ToniBiro/WALL-E/3D Parts/Other/crateCornerSmall v2.stl

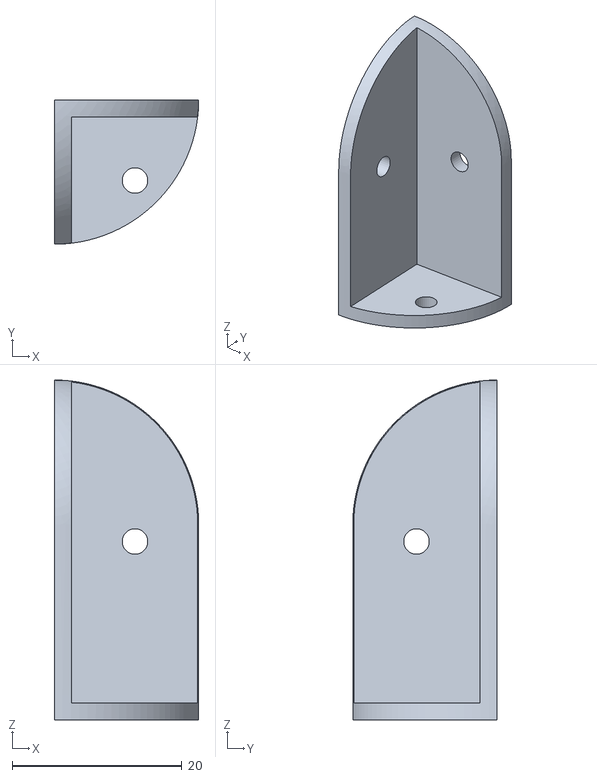
[picture p29: CAD file, 2020-02-20]
3D Parts/Other/crateCornerSmall v2.stl
17.0 x 17.0 x 40.0
