ToniBiro/WALL-E/3D Parts/Other/Text/dot.stl

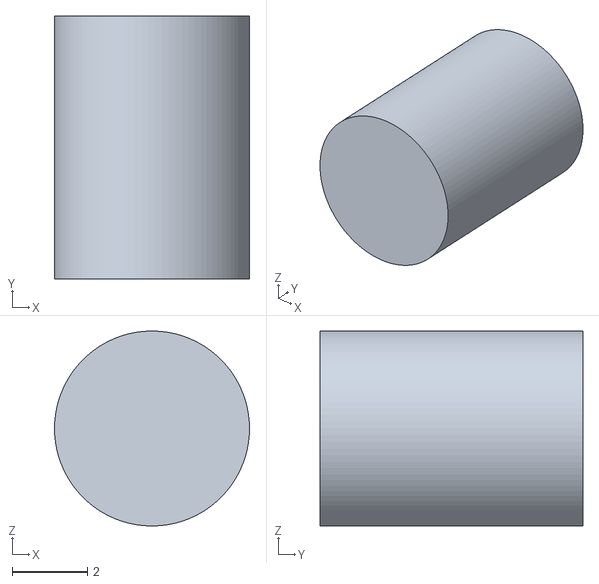
[picture p30: CAD file, 2020-02-20]
3D Parts/Other/Text/dot.stl
5.19 x 7.00 x 5.19
