ToniBiro/WALL-E/3D Parts/Tracks/TractionGear.stl

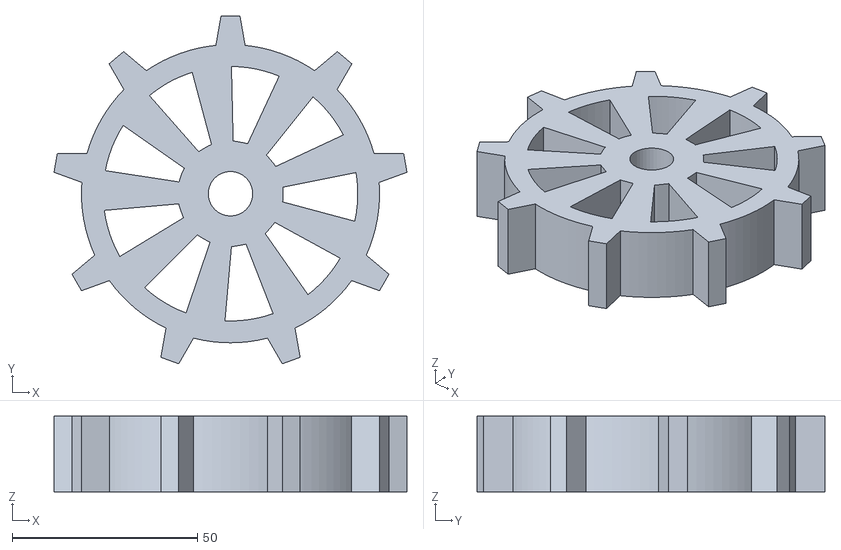
[picture p31: CAD file, 2020-02-19]
3D Parts/Tracks/TractionGear.stl
95.3 x 93.8 x 20.5
