ToniBiro/WALL-E/3D Parts/Arm/ArmMotorHolder.stl

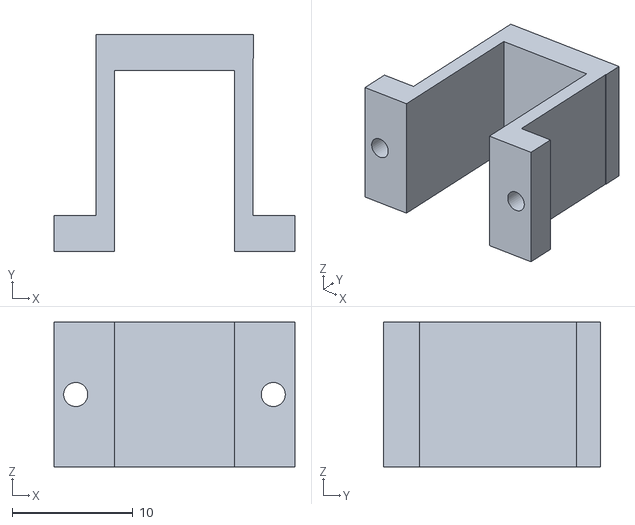
[picture p32: CAD file, 2020-02-19]
3D Parts/Arm/ArmMotorHolder.stl
20.0 x 18.0 x 12.0
