ToniBiro/WALL-E/3D Parts/Compression/FloorWithHinge.stl

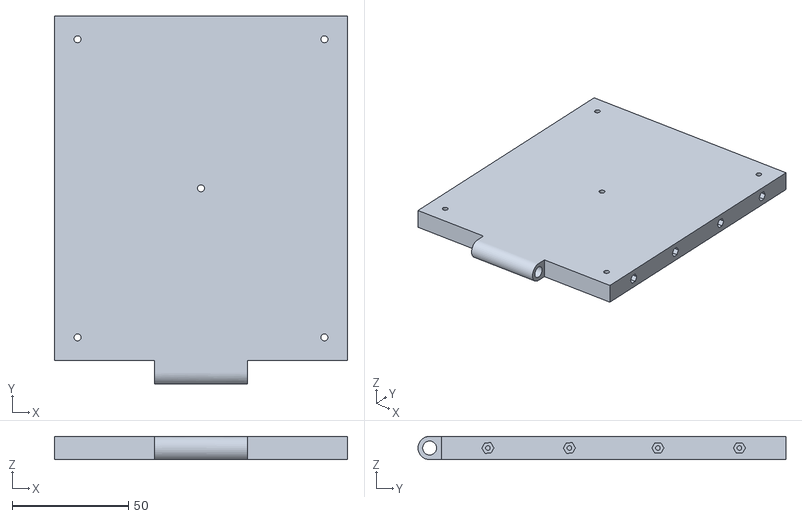
[picture p33: CAD file, 2020-02-19]
3D Parts/Compression/FloorWithHinge.stl
126.0 x 158.0 x 10.0
