ToniBiro/WALL-E/3D Parts/Hand/ConnectionToCilinder.stl

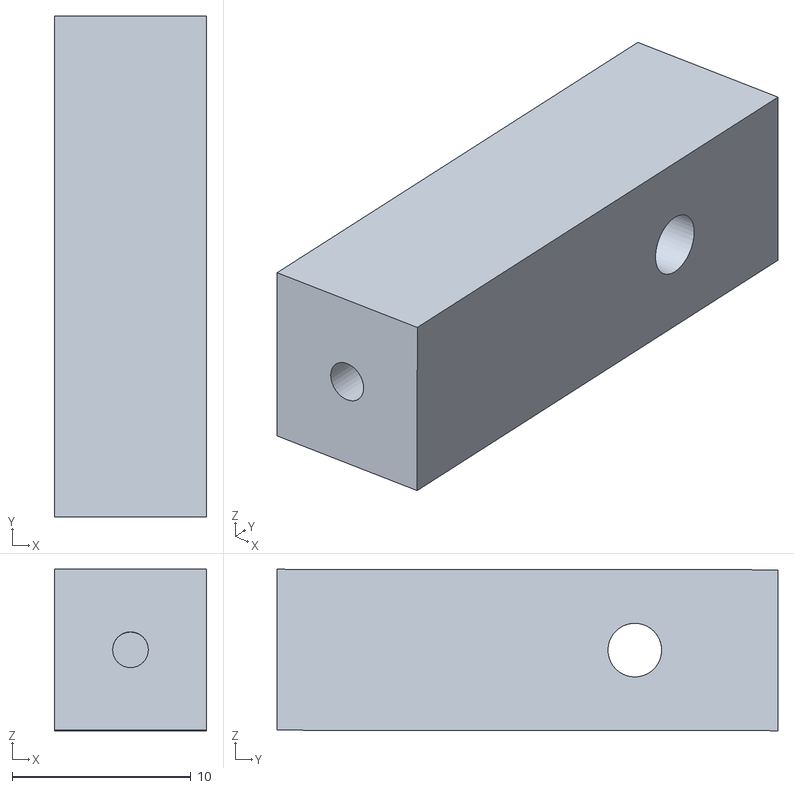
[picture p34: CAD file, 2020-02-19]
3D Parts/Hand/ConnectionToCilinder.stl
8.50 x 28.0 x 9.03
