ToniBiro/WALL-E/3D Parts/Head/connectionCilinderSide.stl

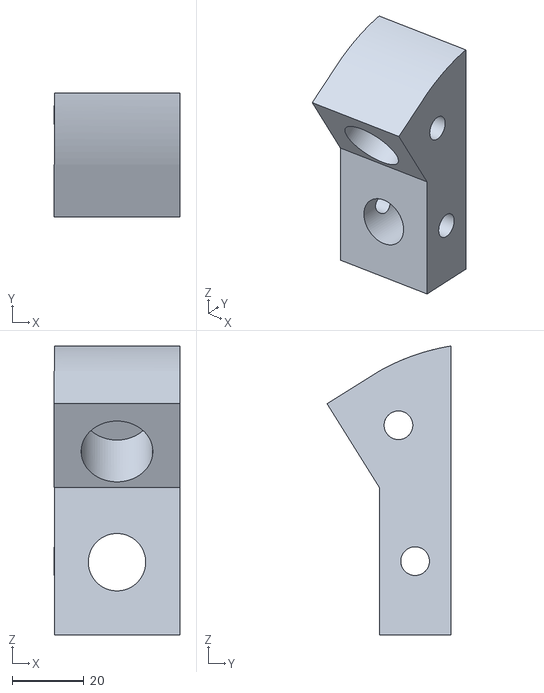
[picture p35: CAD file, 2020-02-19]
3D Parts/Head/connectionCilinderSide.stl
35.0 x 34.6 x 80.6
