ToniBiro/WALL-E/3D Parts/Other/Text/W.stl

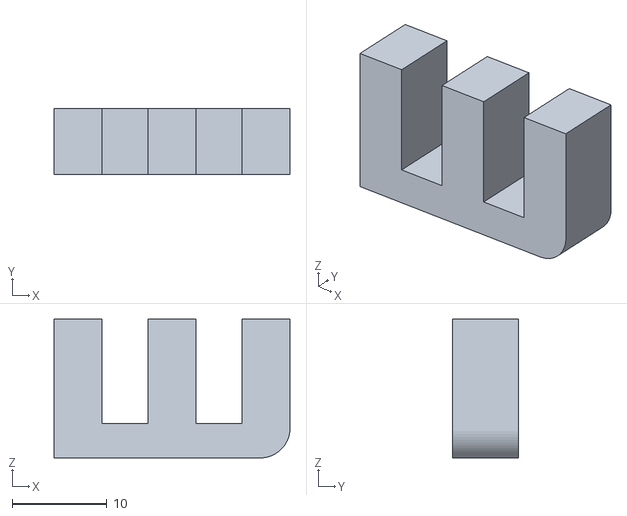
[picture p36: CAD file, 2020-02-20]
3D Parts/Other/Text/W.stl
24.9 x 7.00 x 14.6
