ToniBiro/WALL-E/3D Parts/Tracks/trackPiece.stl

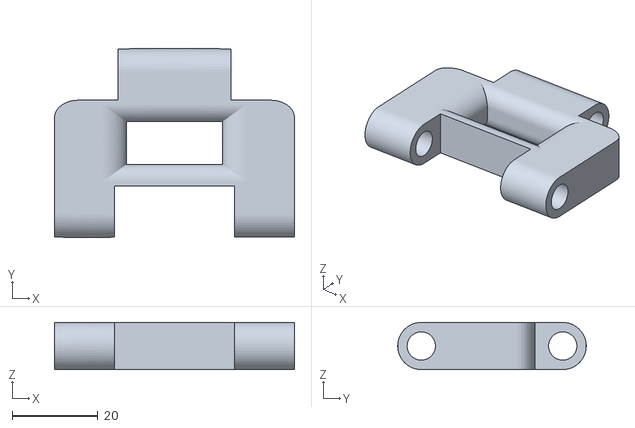
[picture p37: CAD file, 2020-02-19]
3D Parts/Tracks/trackPiece.stl
56.0 x 44.0 x 11.0
