ToniBiro/WALL-E/3D Parts/Arm/MotorCoupling.stl

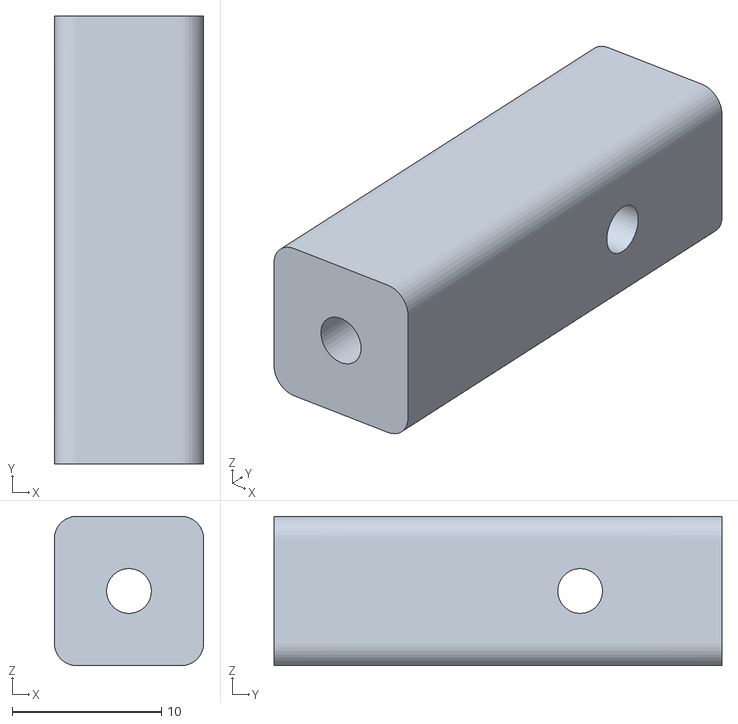
[picture p38: CAD file, 2020-02-19]
3D Parts/Arm/MotorCoupling.stl
10.0 x 30.0 x 10.0
