ToniBiro/WALL-E/3D Parts/Hand/ThirdFinger.stl

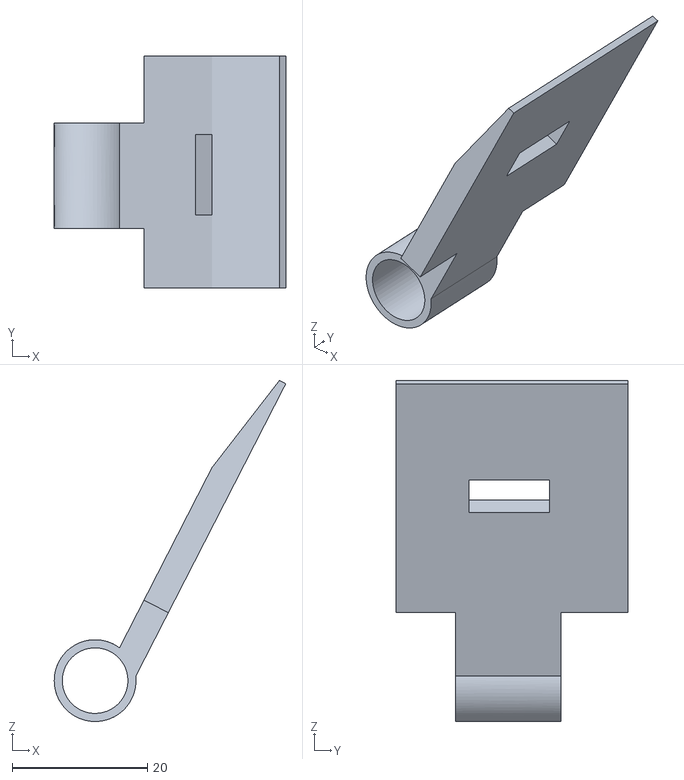
[picture p40: CAD file, 2020-02-19]
3D Parts/Hand/ThirdFinger.stl
34.2 x 34.2 x 50.3
