ToniBiro/WALL-E/3D Parts/Head/connection.stl

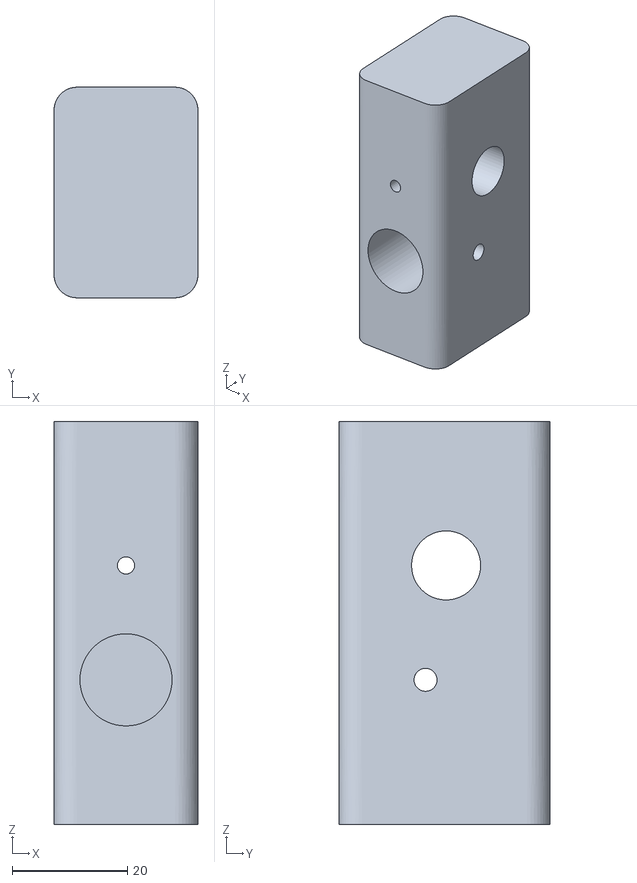
[picture p41: CAD file, 2020-02-19]
3D Parts/Head/connection.stl
25.0 x 36.6 x 70.0
