ToniBiro/WALL-E/3D Parts/Other/Text/L.stl

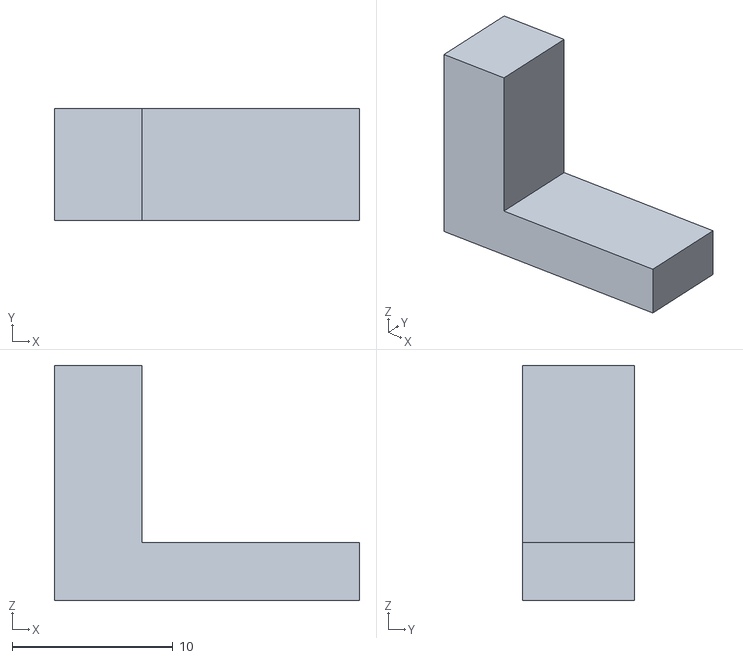
[picture p42: CAD file, 2020-02-20]
3D Parts/Other/Text/L.stl
19.0 x 7.00 x 14.6
