ToniBiro/WALL-E/3D Parts/Tracks/reinforcementTrackGuard.stl

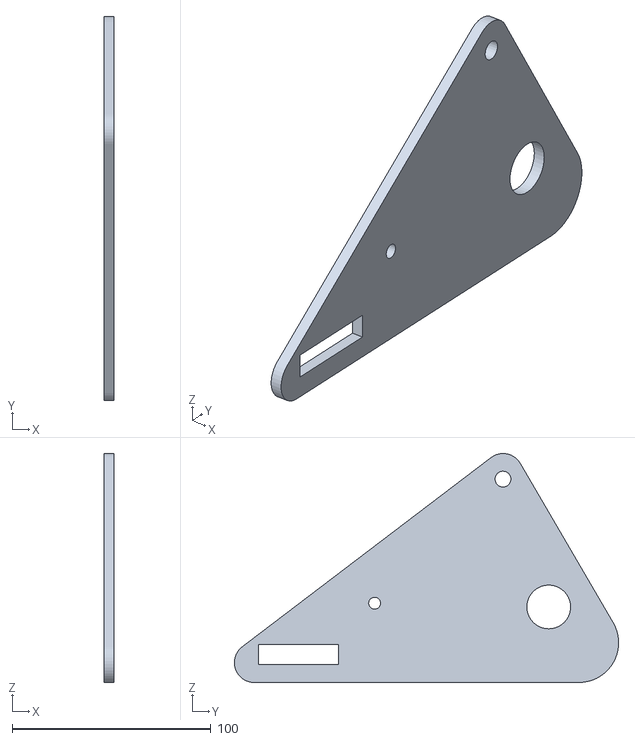
[picture p43: CAD file, 2020-02-19]
3D Parts/Tracks/reinforcementTrackGuard.stl
5.00 x 193.3 x 115.2
