ToniBiro/WALL-E/3D Parts/Arm/LeftArmCoup.stl

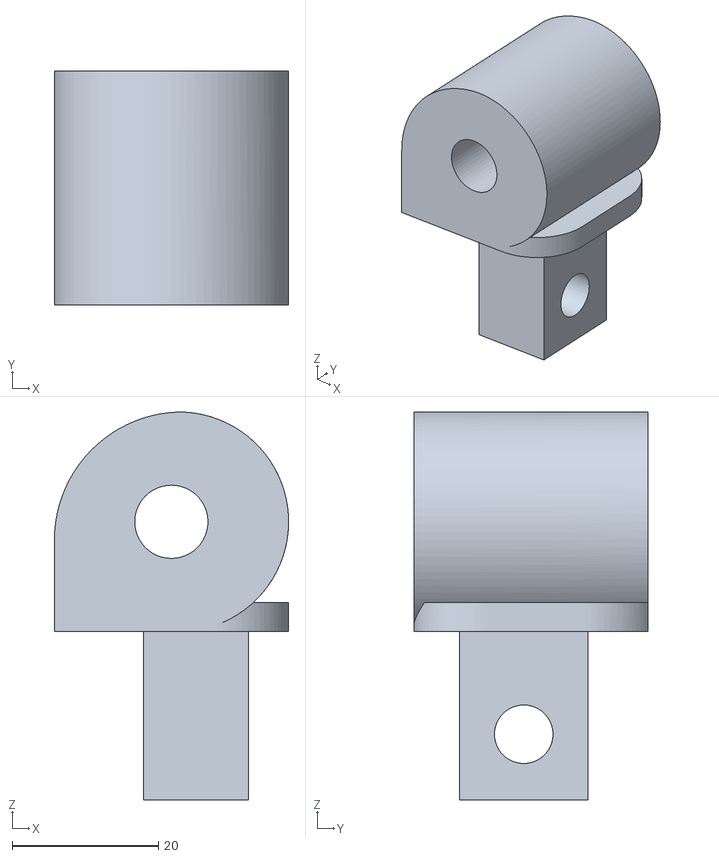
[picture p44: CAD file, 2020-02-19]
3D Parts/Arm/LeftArmCoup.stl
32.0 x 32.0 x 53.0
