ToniBiro/WALL-E/3D Parts/Compression/leftWall.stl

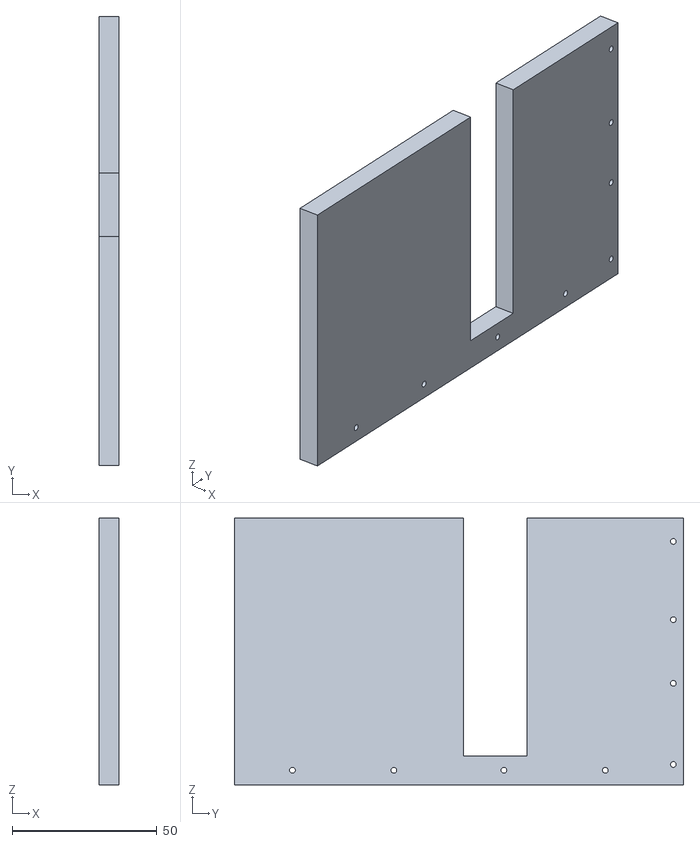
[picture p45: CAD file, 2020-02-19]
3D Parts/Compression/leftWall.stl
7.00 x 155.0 x 92.0
