ToniBiro/WALL-E/3D Parts/Head/bodyConnection.stl

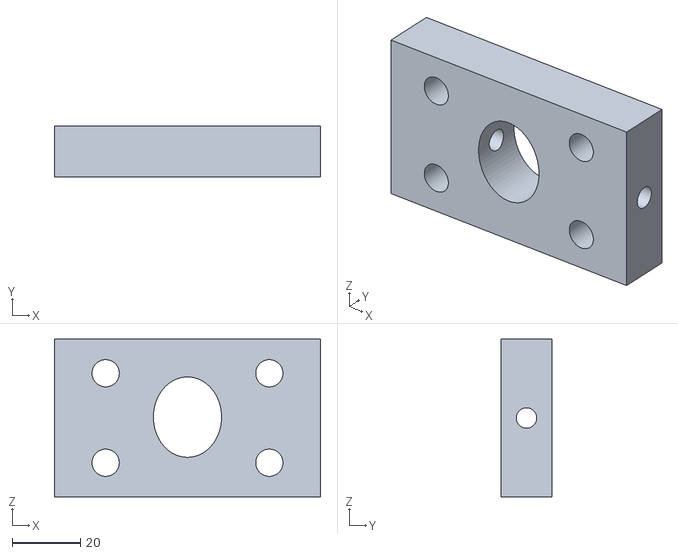
[picture p46: CAD file, 2020-02-19]
3D Parts/Head/bodyConnection.stl
78.0 x 15.0 x 46.2
