ToniBiro/WALL-E/3D Parts/Other/Text/E.stl

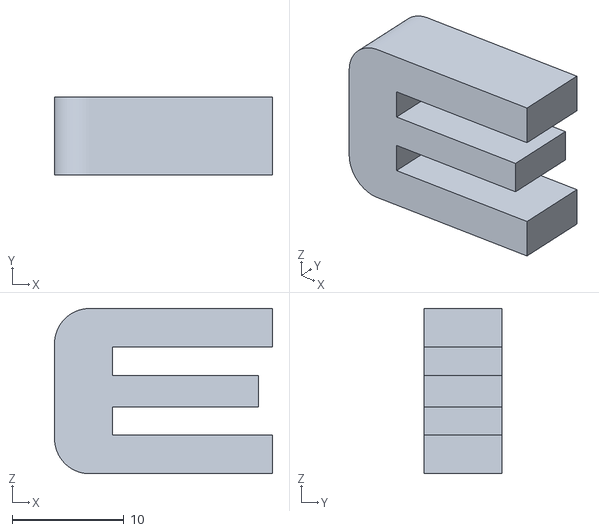
[picture p47: CAD file, 2020-02-20]
3D Parts/Other/Text/E.stl
19.5 x 7.00 x 14.8
