ToniBiro/WALL-E/3D Parts/Tracks/Gearbox Spur Gear (10 teeth).stl

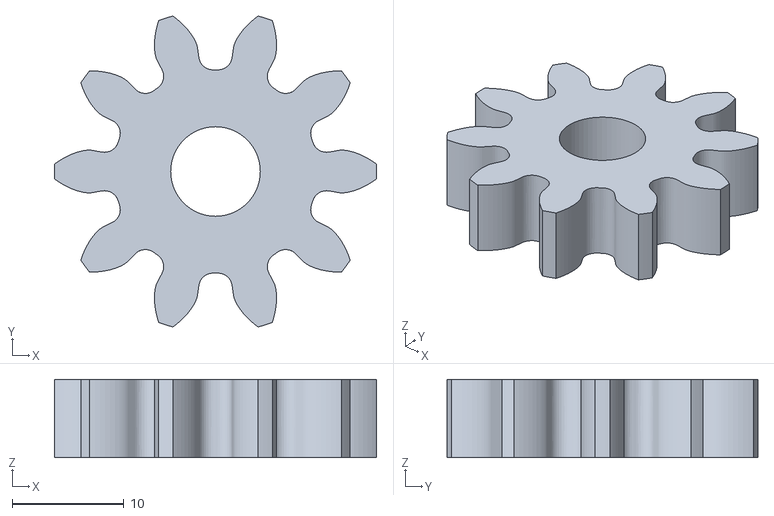
[picture p48: CAD file, 2020-02-19]
3D Parts/Tracks/Gearbox Spur Gear (10 teeth).stl
28.8 x 27.8 x 7.00
