ToniBiro/WALL-E/3D Parts/Arm/RightArmright.stl

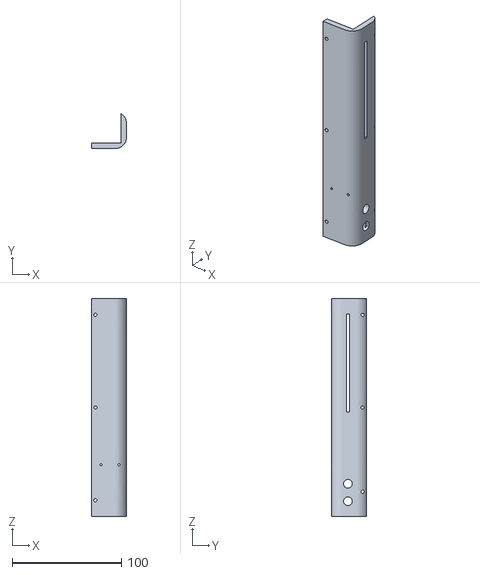
[picture p49: CAD file, 2020-02-19]
3D Parts/Arm/RightArmright.stl
32.0 x 32.0 x 200.0
