ToniBiro/WALL-E/3D Parts/Compression/timingBeltGearStepper.stl

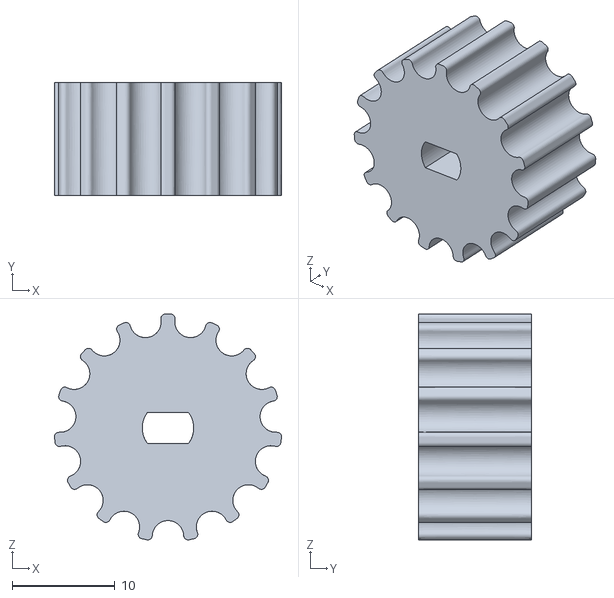
[picture p50: CAD file, 2020-02-19]
3D Parts/Compression/timingBeltGearStepper.stl
22.1 x 11.0 x 21.9
