ToniBiro/WALL-E/3D Parts/Other/Text/redCircle.stl

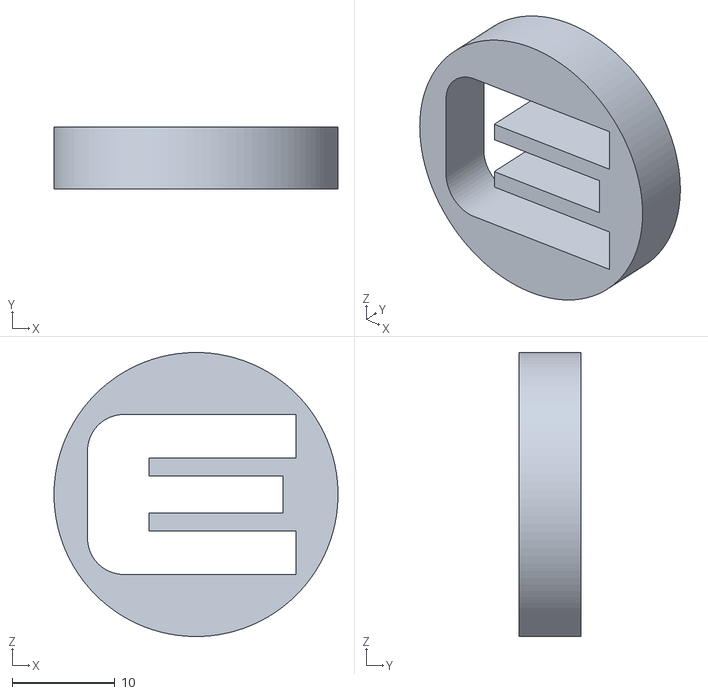
[picture p51: CAD file, 2020-02-20]
3D Parts/Other/Text/redCircle.stl
27.7 x 6.00 x 27.7
