ToniBiro/WALL-E/3D Parts/Tracks/SmallTrackGear.stl

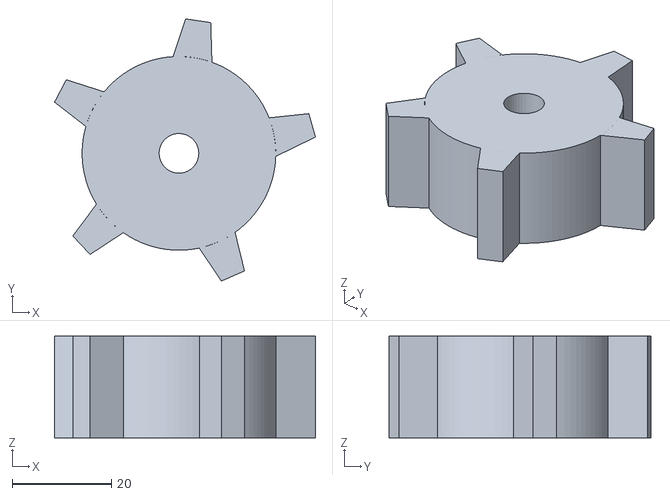
[picture p52: CAD file, 2020-02-19]
3D Parts/Tracks/SmallTrackGear.stl
52.6 x 52.9 x 20.5
