ToniBiro/WALL-E/3D Parts/Compression/backWall.stl

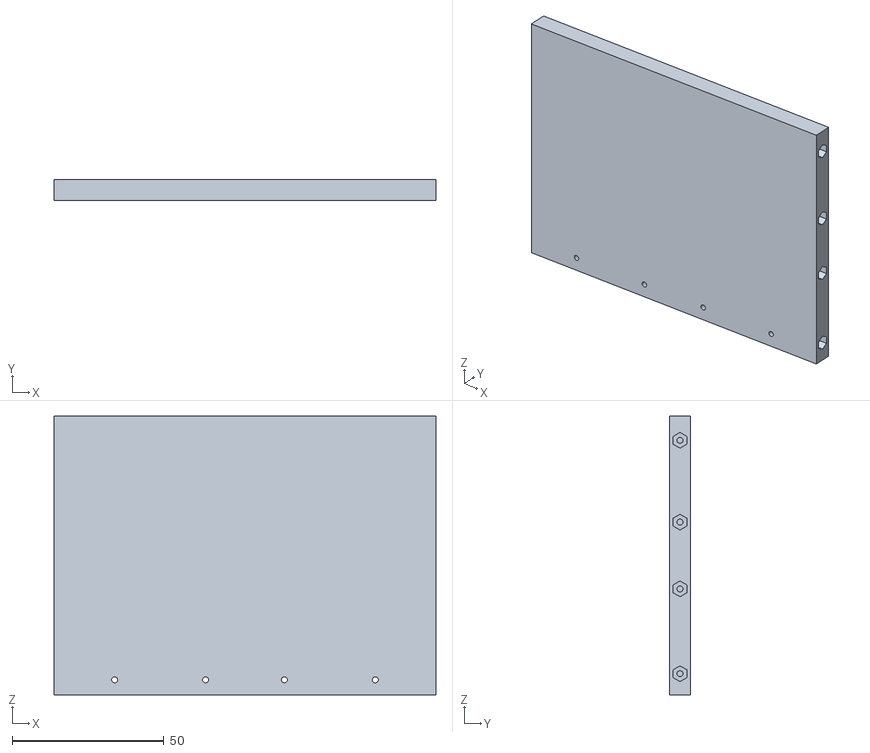
[picture p53: CAD file, 2020-02-19]
3D Parts/Compression/backWall.stl
126.0 x 7.00 x 92.0
