ToniBiro/WALL-E/3D Parts/Arm/RightArmleft.stl

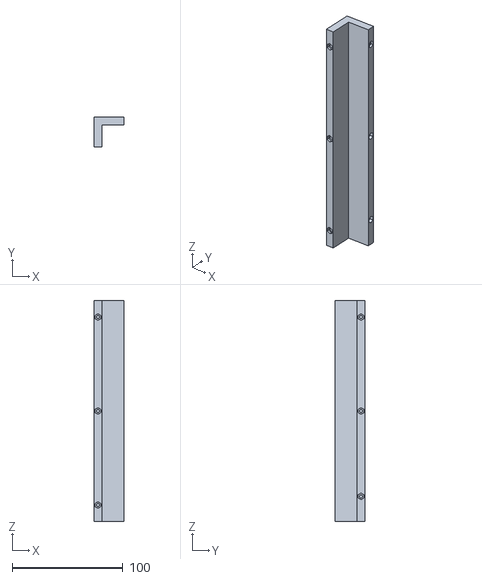
[picture p54: CAD file, 2020-02-19]
3D Parts/Arm/RightArmleft.stl
27.0 x 27.0 x 200.0
