ToniBiro/WALL-E/3D Parts/Compression/Sliding Door Spur Gear (8 teeth).stl

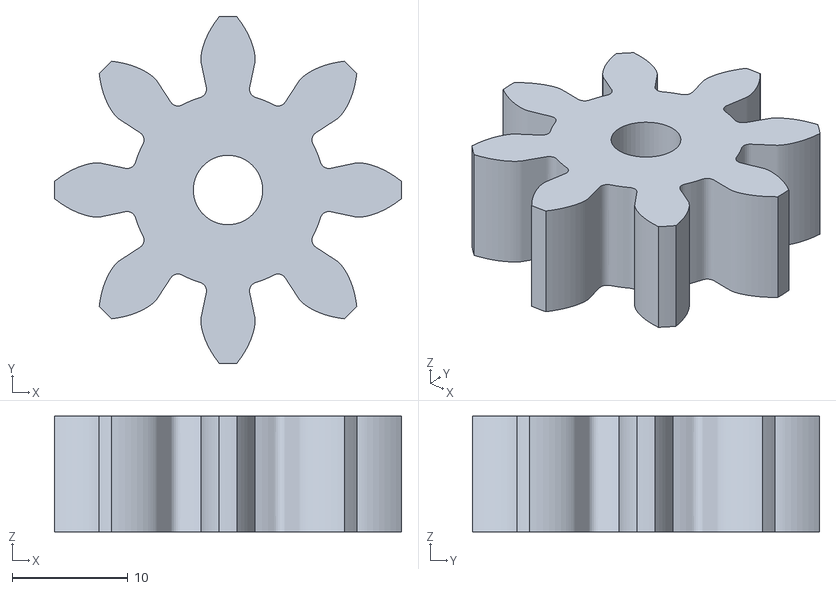
[picture p55: CAD file, 2020-02-19]
3D Parts/Compression/Sliding Door Spur Gear (8 teeth).stl
30.0 x 30.0 x 10.0
