ToniBiro/WALL-E/3D Parts/Compression/DoorVerticalStepperSlider.stl

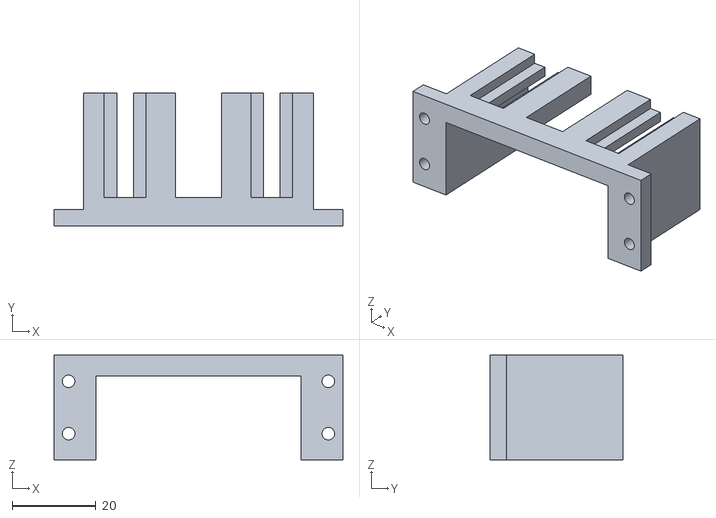
[picture p56: CAD file, 2020-02-19]
3D Parts/Compression/DoorVerticalStepperSlider.stl
69.0 x 31.9 x 25.0
