ToniBiro/WALL-E/3D Parts/Compression/slidingDoor.stl

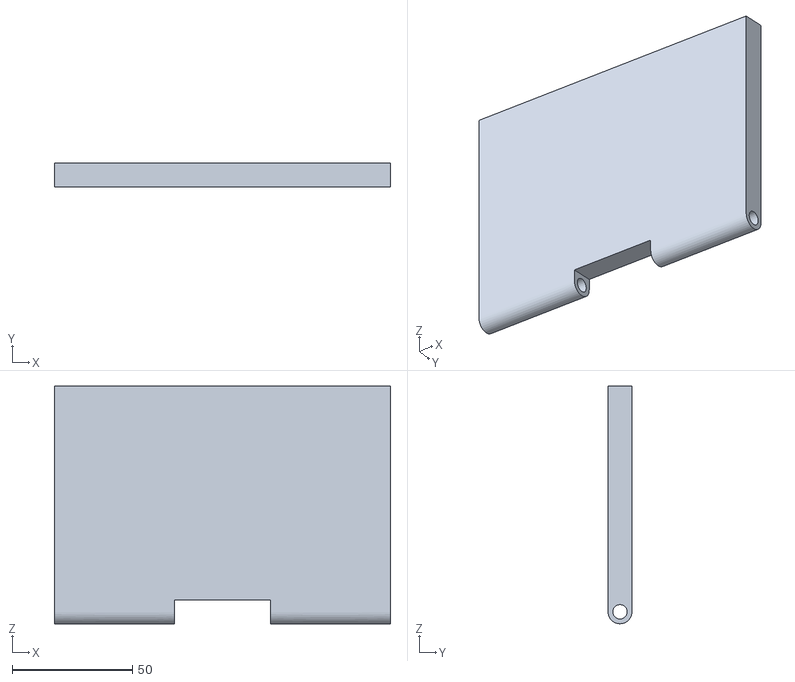
[picture p57: CAD file, 2020-02-19]
3D Parts/Compression/slidingDoor.stl
140.0 x 10.0 x 99.0
