ToniBiro/WALL-E/3D Parts/Arm/servoVerticalHolder.stl

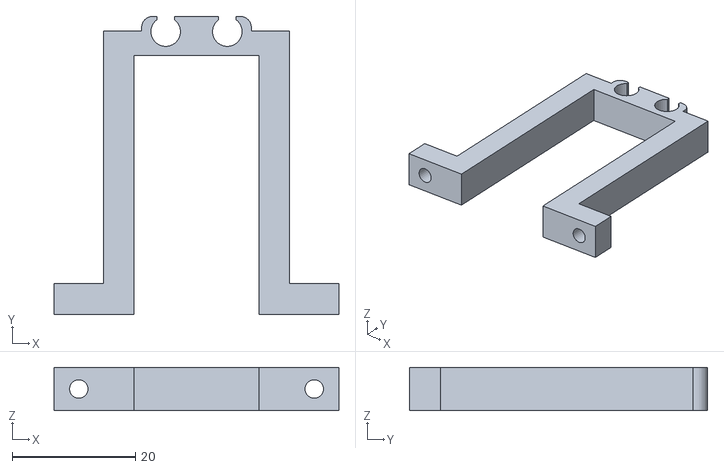
[picture p58: CAD file, 2020-02-19]
3D Parts/Arm/servoVerticalHolder.stl
46.2 x 48.4 x 7.00
