ToniBiro/WALL-E/3D Parts/Compression/Sliding Door Spur Gear (16 teeth).stl

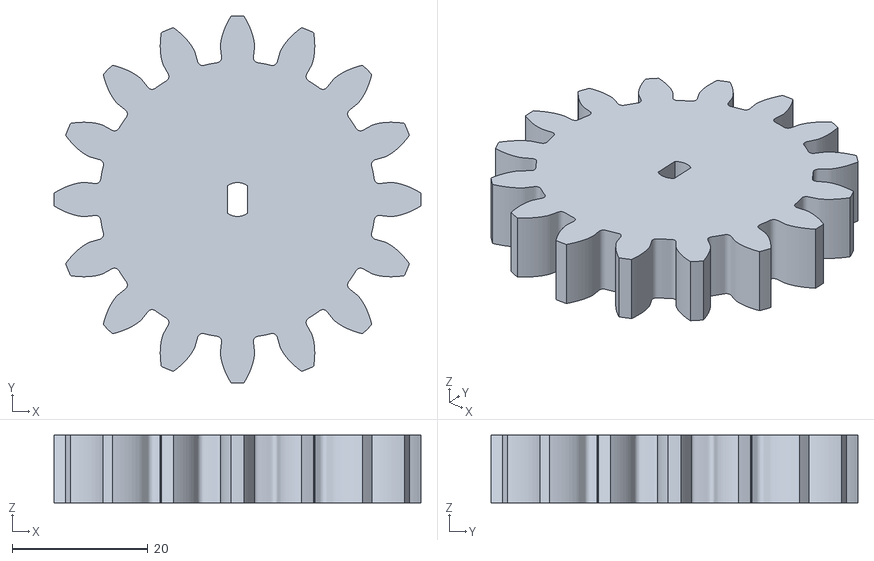
[picture p59: CAD file, 2020-02-19]
3D Parts/Compression/Sliding Door Spur Gear (16 teeth).stl
54.0 x 54.0 x 10.0
